Ans1S/esp32-c3-iot-sensor-board/Firmware/sensor/include/environmental_sensor.h

#pragma once

#include "lsm6dsox_driver.h"
#include "precision_sensors.h"
#include "bme280_driver.h"
#include "bme680_driver.h"
#include "environmental_reading.h"
#include "power_controller.h"

namespace sensor {

class EnvironmentalSensor {
 public:
  bool begin(PowerController& power,
             lil::protocol::EnvironmentalSensorType requestedType,
             float temperatureOffsetC);
  EnvironmentalReading read();
  bool pollLive() { return detectedType_ == lil::protocol::EnvironmentalSensorType::kLsm6dsox ? lsm6dsox_.poll() : precision_.poll(); }
  bool freshTemperature() const { return precision_.freshTemperature(); }
  void resetMotionFeedback() { lsm6dsox_.resetFeedback(); }
  void end();
  void prepareForDeepSleep(
      uint32_t seconds,
      lil::protocol::EnvironmentalSensorType activeType =
          lil::protocol::EnvironmentalSensorType::kAutoDetect);
  uint32_t bme680RecommendedSleepSeconds(uint32_t fallbackSeconds) const;
  bool clearIaqState();
  lil::protocol::EnvironmentalSensorType detectedType() const;

 private:
  lil::protocol::EnvironmentalSensorType probeSensorType(uint8_t& address) const;
  bool startDetectedSensor(
      lil::protocol::EnvironmentalSensorType requestedType,
      float temperatureOffsetC);
  bool beginType(lil::protocol::EnvironmentalSensorType type,
                 uint8_t address, float temperatureOffsetC);

  PowerController* power_ = nullptr;
  Lsm6dsoxDriver lsm6dsox_;
  PrecisionSensors precision_;
  Bme280Driver bme280_;
  Bme680Driver bme680_;
  lil::protocol::EnvironmentalSensorType requestedType_ =
      lil::protocol::EnvironmentalSensorType::kAutoDetect;
  lil::protocol::EnvironmentalSensorType detectedType_ =
      lil::protocol::EnvironmentalSensorType::kAutoDetect;
  bool initialized_ = false;
  bool typeMismatch_ = false;
};

}  // namespace sensor
