Ans1S/esp32-c3-iot-sensor-board/Firmware/station/src/web_portal.cpp

#include "web_portal.h"
#include "recording_json.h"
#include "ota_service.h"
#include "ota_page.h"
#include "recording_archive.h"
#include <memory>

#include <ArduinoJson.h>
#include <SHA2Builder.h>
#include <esp_heap_caps.h>
#include <esp_random.h>
#include <esp_timer.h>

#include "web_pages.h"
#include "web_input.h"

namespace station {

namespace {
constexpr size_t kMaxScannedNetworks = 20;
constexpr char kSessionCookieName[] = "wch_session";
constexpr char kPasswordHashDomain[] = "W-Charger website password v1";
constexpr uint8_t kMaxLoginAttempts = 5;
constexpr uint32_t kLoginBlockMs = 30000;
constexpr uint32_t kLoginAttemptWindowMs = 5UL * 60UL * 1000UL;
constexpr uint64_t kSessionLifetimeMs = 30ULL * 60ULL * 1000ULL;
constexpr uint32_t kSessionLifetimeSeconds = kSessionLifetimeMs / 1000UL;

bool readUnsignedArgument(WebServer& server, const char* name,
                          uint32_t& value, uint32_t minimum = 0,
                          uint32_t maximum = UINT32_MAX,
                          bool optional = false) {
  if (!server.hasArg(name)) return optional;
  return webinput::unsignedDecimal(server.arg(name).c_str(), value,
                                  minimum, maximum);
}

bool readFieldArgument(WebServer& server, const char* name, uint8_t& field) {
  uint32_t value = 0;
  if (!readUnsignedArgument(server, name, value, 0, 8, true)) return false;
  field = static_cast<uint8_t>(value);
  return true;
}

void hashAdminPassword(const String& password, char output[65]) {
  SHA256Builder hash;
  hash.begin();
  const uint64_t deviceId = ESP.getEfuseMac();
  hash.add(reinterpret_cast<const uint8_t*>(kPasswordHashDomain),
           strlen(kPasswordHashDomain));
  hash.add(reinterpret_cast<const uint8_t*>(&deviceId), sizeof(deviceId));
  hash.add(reinterpret_cast<const uint8_t*>(password.c_str()),
           password.length());
  hash.calculate();
  hash.getChars(output);
}

bool constantTimeEquals(const char* first, const char* second,
                        size_t length) {
  uint8_t difference = 0;
  for (size_t i = 0; i < length; ++i) {
    difference |= static_cast<uint8_t>(first[i] ^ second[i]);
  }
  return difference == 0;
}

void randomToken(char output[33]) {
  snprintf(output, 33, "%08lX%08lX%08lX%08lX",
           static_cast<unsigned long>(esp_random()),
           static_cast<unsigned long>(esp_random()),
           static_cast<unsigned long>(esp_random()),
           static_cast<unsigned long>(esp_random()));
}

void appendFormValue(String& body, const char* name, const String& value) {
  if (!body.isEmpty()) {
    body += '&';
  }
  body += name;
  body += '=';
  body += ThingSpeakService::urlEncode(value);
}

void extractApiKeys(JsonObjectConst channel, String& readKey,
                    String& writeKey) {
  for (JsonObjectConst key : channel["api_keys"].as<JsonArrayConst>()) {
    if (key["write_flag"] | false) {
      writeKey = key["api_key"].as<String>();
    } else if (readKey.isEmpty()) {
      readKey = key["api_key"].as<String>();
    }
  }
}

String tagsAsText(JsonVariantConst value) {
  String output;
  for (JsonVariantConst tag : value.as<JsonArrayConst>()) {
    const String name = tag.is<JsonObjectConst>()
                            ? tag["name"].as<String>()
                            : tag.as<String>();
    if (name.isEmpty()) {
      continue;
    }
    if (!output.isEmpty()) {
      output += ", ";
    }
    output += name;
  }
  return output;
}

bool validOptionalDecimal(const String& text, double minimum,
                          double maximum) {
  if (text.isEmpty()) {
    return true;
  }
  char* end = nullptr;
  const double value = strtod(text.c_str(), &end);
  return end != text.c_str() && *end == '\0' && isfinite(value) &&
         value >= minimum && value <= maximum;
}

bool validManagedChannelRequest(WebServer& server) {
  if (server.arg("name").isEmpty() || server.arg("name").length() > 80 ||
      server.arg("description").length() > 255 ||
      server.arg("metadata").length() > 512 ||
      server.arg("tags").length() > 160 || server.arg("url").length() > 200 ||
      !validOptionalDecimal(server.arg("latitude"), -90.0, 90.0) ||
      !validOptionalDecimal(server.arg("longitude"), -180.0, 180.0) ||
      !validOptionalDecimal(server.arg("elevation"), -10000.0, 100000.0)) {
    return false;
  }
  for (uint8_t field = 1; field <= 8; ++field) {
    if (server.arg("field" + String(field)).length() > 80) {
      return false;
    }
  }
  return true;
}

String managedChannelSettings(WebServer& server) {
  String body;
  body.reserve(900);
  appendFormValue(body, "name", server.arg("name"));
  appendFormValue(body, "description", server.arg("description"));
  appendFormValue(body, "metadata", server.arg("metadata"));
  appendFormValue(body, "tags", server.arg("tags"));
  appendFormValue(body, "url", server.arg("url"));
  appendFormValue(body, "latitude", server.arg("latitude"));
  appendFormValue(body, "longitude", server.arg("longitude"));
  appendFormValue(body, "elevation", server.arg("elevation"));
  appendFormValue(body, "public_flag",
                  server.hasArg("publicFlag") ? "true" : "false");
  for (uint8_t field = 1; field <= 8; ++field) {
    const String key = "field" + String(field);
    appendFormValue(body, key.c_str(), server.arg(key));
  }
  return body;
}

bool validThingSpeakFields(const ThingSpeakFieldMapping& fields,
                           bool requireOne) {
  const uint8_t values[] = {fields.temperature, fields.humidity,
                            fields.pressure, fields.iaq, fields.battery,
                            fields.gasResistance};
  constexpr size_t count = sizeof(values) / sizeof(values[0]);
  bool hasField = false;
  for (size_t i = 0; i < count; ++i) {
    if (values[i] > 8) {
      return false;
    }
    if (values[i] == 0) {
      continue;
    }
    hasField = true;
    for (size_t j = i + 1; j < count; ++j) {
      if (values[i] == values[j]) {
        return false;
      }
    }
  }
  return hasField || !requireOne;
}

void sendNoCache(WebServer& server) {
  server.sendHeader("Cache-Control", "no-store, no-cache, must-revalidate");
  server.sendHeader("Pragma", "no-cache");
  server.sendHeader("X-Content-Type-Options", "nosniff");
  server.sendHeader("X-Frame-Options", "DENY");
  server.sendHeader("Referrer-Policy", "no-referrer");
  server.sendHeader("Permissions-Policy",
                    "camera=(), microphone=(), geolocation=()");
  server.sendHeader("Cross-Origin-Resource-Policy", "same-origin");
  server.sendHeader(
      "Content-Security-Policy",
      "default-src 'self'; style-src 'self' 'unsafe-inline'; script-src "
      "'self' 'unsafe-inline'; img-src 'self' data:; connect-src 'self'; "
      "object-src 'none'; frame-ancestors 'none'; base-uri 'none'; "
      "form-action 'self'");
}
}  // namespace

bool WebPortal::begin(StationConfig& config, ConfigStore& store,
                      WifiService& wifi, SensorRegistry& registry,
                      ThingSpeakService& thingSpeak, EspNowGateway& gateway) {
  config_ = &config;
  store_ = &store;
  wifi_ = &wifi;
  registry_ = &registry;
  thingSpeak_ = &thingSpeak;
  gateway_ = &gateway;
  refreshCsrfToken();
  clearAuthSessions();
  const char* collectedHeaders[] = {"Cookie", "Origin"};
  server_.collectHeaders(collectedHeaders, 2);

  server_.on("/", HTTP_GET, [this]() {
    sendNoCache(server_);
    if (config_->wifiSsid[0] != '\0' && !requireAuthentication(true)) {
      return;
    }
    server_.send_P(200, "text/html; charset=utf-8",
                   config_->wifiSsid[0] == '\0' ? kSetupWizardPage
                                                : kDashboardPage);
  });
  server_.on("/setup", HTTP_GET, [this]() {
    sendNoCache(server_);
    if (config_->wifiSsid[0] != '\0') {
      server_.sendHeader("Location", "/dashboard", true);
      server_.send(302, "text/plain", "");
      return;
    }
    server_.send_P(200, "text/html; charset=utf-8", kSetupWizardPage);
  });
  server_.on("/dashboard", HTTP_GET, [this]() {
    sendNoCache(server_);
    if (!requireAuthentication(true)) {
      return;
    }
    server_.send_P(200, "text/html; charset=utf-8", kDashboardPage);
  });
  server_.on("/login", HTTP_GET, [this]() { handleLogin(); });
  server_.on("/login", HTTP_POST, [this]() { handleLogin(); });
  server_.on("/logout", HTTP_POST, [this]() {
    if (requireAuthentication() && verifyCsrf()) handleLogout();
  });
  server_.on("/api/status", HTTP_GET, [this]() {
    if (requireAuthentication()) sendJsonStatus();
  });
  server_.on("/api/ota", HTTP_GET, [this]() {
    if (!requireAuthentication()) return;
    JsonDocument doc;
    otaService.json(doc.to<JsonObject>());
    String body; serializeJson(doc, body);
    sendNoCache(server_); server_.send(200, "application/json", body);
  });
  server_.on("/updates", HTTP_GET, [this]() {
    if (!requireAuthentication(true)) return;
    sendNoCache(server_); server_.send_P(200, "text/html; charset=utf-8", kOtaPage);
  });
  server_.on("/api/ota/cancel", HTTP_POST, [this]() {
    if (requireAuthentication() && verifyCsrf())
      sendJsonResult(otaService.cancel(), "Update cancellation saved; a reboot already initiated cannot be cancelled");
  });
  server_.on("/api/ota/upload", HTTP_POST, [this]() {
    if (!otaUploadAuthorized_) return;
    sendJsonResult(otaUploadOk_, otaUploadOk_ ? "Update queued for the next node contact" : otaUploadError_);
    otaUploadAuthorized_ = false;
  }, [this]() {
    HTTPUpload& upload = server_.upload();
    if (upload.status == UPLOAD_FILE_START) {
      otaUploadAuthorized_ = requireAuthentication() && verifyCsrf();
      otaUploadOk_ = false; otaUploadError_ = "Upload failed";
      if (!otaUploadAuthorized_) return;
      uint8_t mac[6];
      if (!SensorRegistry::parseMac(server_.arg("mac"), mac)) {
        otaUploadError_ = "Invalid node address"; return;
      }
      SensorConfig node{};
      if (!registry_->findConfig(mac, node) || !node.provisioned) {
        otaUploadError_ = "Select a configured node"; return;
      }
      otaUploadOk_ = otaService.startUpload(mac, otaUploadError_);
    } else if (upload.status == UPLOAD_FILE_WRITE && otaUploadAuthorized_ && otaUploadOk_) {
      if (!otaService.upload(upload.buf, upload.currentSize)) {
        otaUploadOk_ = false; otaUploadError_ = "Firmware exceeds capacity or flash write failed";
        otaService.abortUpload();
      }
    } else if (upload.status == UPLOAD_FILE_END && otaUploadAuthorized_ && otaUploadOk_) {
      otaUploadOk_ = otaService.finishUpload(otaUploadError_);
    } else if (upload.status == UPLOAD_FILE_ABORTED && otaUploadAuthorized_) {
      otaService.abortUpload(); otaUploadOk_ = false;
    }
  });
  server_.on("/api/history", HTTP_GET, [this]() {
    if (requireAuthentication()) sendJsonHistory();
  });
  server_.on("/api/recordings", HTTP_GET, [this]() { if (requireAuthentication()) sendRecordings(); });
  server_.on("/api/recording", HTTP_GET, [this]() { if (requireAuthentication()) sendRecording(); });
  server_.on("/api/motion-reference", HTTP_POST, [this]() { if (requireAuthentication() && verifyCsrf()) setMotionReference(); });
  server_.on("/api/recording/delete", HTTP_POST, [this]() {
    if (requireAuthentication() && verifyCsrf()) deleteRecording();
  });
  server_.on("/api/config", HTTP_GET, [this]() {
    if (requireAuthentication()) sendJsonConfig();
  });
  server_.on("/api/wifi-scan", HTTP_GET, [this]() {
    if (requireAuthentication()) sendWifiScan();
  });
  server_.on("/api/setup", HTTP_POST, [this]() {
    if (requireAuthentication() && verifyCsrf()) saveSetup();
  });
  server_.on("/api/setup-sensor", HTTP_POST, [this]() {
    if (requireAuthentication() && verifyCsrf()) saveSetupSensor();
  });
  server_.on("/api/station", HTTP_POST, [this]() {
    if (requireAuthentication() && verifyCsrf()) saveStation();
  });
  server_.on("/api/sensor", HTTP_POST, [this]() {
    if (requireAuthentication() && verifyCsrf()) saveSensor();
  });
  server_.on("/api/channel-profile", HTTP_POST, [this]() {
    if (requireAuthentication() && verifyCsrf()) saveChannelProfile();
  });
  server_.on("/api/delete-channel-profile", HTTP_POST, [this]() {
    if (requireAuthentication() && verifyCsrf()) deleteChannelProfile();
  });
  server_.on("/api/create-channel", HTTP_POST, [this]() {
    if (requireAuthentication() && verifyCsrf()) createThingSpeakChannel();
  });
  server_.on("/api/thingspeak/channels", HTTP_GET, [this]() {
    if (requireAuthentication()) listThingSpeakChannels();
  });
  server_.on("/api/thingspeak/channel-create", HTTP_POST, [this]() {
    if (requireAuthentication() && verifyCsrf())
      createManagedThingSpeakChannel();
  });
  server_.on("/api/thingspeak/channel-update", HTTP_POST, [this]() {
    if (requireAuthentication() && verifyCsrf())
      updateManagedThingSpeakChannel();
  });
  server_.on("/api/thingspeak/channel-clear", HTTP_POST, [this]() {
    if (requireAuthentication() && verifyCsrf())
      clearManagedThingSpeakChannel();
  });
  server_.on("/api/thingspeak/channel-delete", HTTP_POST, [this]() {
    if (requireAuthentication() && verifyCsrf())
      deleteManagedThingSpeakChannel();
  });
  server_.on("/api/reset-sensor", HTTP_POST, [this]() {
    if (requireAuthentication() && verifyCsrf()) resetSensor();
  });
  server_.on("/api/reset-sensor-iaq", HTTP_POST, [this]() {
    if (requireAuthentication() && verifyCsrf()) resetSensorIaqCalibration();
  });
  server_.on("/api/delete-sensor", HTTP_POST, [this]() {
    if (requireAuthentication() && verifyCsrf()) deleteSensor();
  });
  server_.on("/api/factory-reset", HTTP_POST, [this]() {
    if (requireAuthentication() && verifyCsrf()) factoryReset();
  });
  server_.on("/favicon.ico", HTTP_GET, [this]() {
    sendNoCache(server_);
    server_.send(204, "text/plain", "");
  });

  const auto captiveRedirect = [this]() {
    sendNoCache(server_);
    server_.sendHeader("Connection", "close");
    server_.sendHeader("Location", "/", true);
    server_.send(302, "text/plain", "");
  };
  server_.on("/generate_204", HTTP_ANY, captiveRedirect);
  server_.on("/gen_204", HTTP_ANY, captiveRedirect);
  server_.on("/hotspot-detect.html", HTTP_ANY, captiveRedirect);
  server_.on("/library/test/success.html", HTTP_ANY, captiveRedirect);
  server_.on("/fwlink", HTTP_ANY, captiveRedirect);
  server_.on("/connecttest.txt", HTTP_ANY, captiveRedirect);
  server_.on("/redirect", HTTP_ANY, captiveRedirect);
  server_.on("/canonical.html", HTTP_ANY, captiveRedirect);
  server_.on("/success.txt", HTTP_ANY, captiveRedirect);
  server_.on("/ncsi.txt", HTTP_ANY, captiveRedirect);
  // Common HTTP-only connectivity probes. HTTPS probes cannot be redirected
  // safely because the device does not own their TLS certificates; users can
  // always open http://192.168.4.1/ directly in that case.
  server_.on("/connectivity-check.html", HTTP_ANY, captiveRedirect);
  server_.on("/check_network_status.txt", HTTP_ANY, captiveRedirect);
  server_.on("/portal.html", HTTP_ANY, captiveRedirect);
  server_.on("/success.html", HTTP_ANY, captiveRedirect);
  server_.on("/wifi/wifidog", HTTP_ANY, captiveRedirect);
  server_.on("/kindle-wifi/wifistub.html", HTTP_ANY, captiveRedirect);
  server_.on("/.well-known/captive-portal", HTTP_ANY, captiveRedirect);
  server_.onNotFound([this, captiveRedirect]() {
    const bool apiPath = server_.uri().startsWith("/api/");
    if (apiPath ||
        (config_->wifiSsid[0] != '\0' && !wifi_->setupPortalActive())) {
      sendNoCache(server_);
      server_.send(404, apiPath ? "application/json" : "text/plain",
                   apiPath
                       ? "{\"success\":false,\"message\":\"Not found\"}"
                       : "Not found");
      return;
    }
    captiveRedirect();
  });
  server_.begin();
  return true;
}

bool WebPortal::authenticationEnabled() const {
  return config_ != nullptr && config_->adminPassword[0] != '\0';
}

String WebPortal::currentSessionToken() const {
  const String cookies = server_.header("Cookie");
  const String prefix = String(kSessionCookieName) + '=';
  int start = 0;
  while (start < static_cast<int>(cookies.length())) {
    int end = cookies.indexOf(';', start);
    if (end < 0) {
      end = cookies.length();
    }
    String cookie = cookies.substring(start, end);
    cookie.trim();
    if (cookie.startsWith(prefix)) {
      return cookie.substring(prefix.length());
    }
    start = end + 1;
  }
  return String();
}

bool WebPortal::isAuthenticated() {
  if (!authenticationEnabled()) {
    return true;
  }
  const String token = currentSessionToken();
  if (token.length() != 32) {
    return false;
  }
  const uint64_t now = static_cast<uint64_t>(esp_timer_get_time()) / 1000ULL;
  for (AuthSession& session : authSessions_) {
    if (!session.active) {
      continue;
    }
    if (now - session.createdAtMs >= kSessionLifetimeMs) {
      session = AuthSession{};
      continue;
    }
    if (constantTimeEquals(token.c_str(), session.token, 32)) {
      return true;
    }
  }
  return false;
}

bool WebPortal::requireAuthentication(bool redirectToLogin) {
  if (isAuthenticated()) {
    return true;
  }
  sendNoCache(server_);
  if (redirectToLogin) {
    server_.sendHeader("Location", "/login", true);
    server_.send(302, "text/plain", "");
  } else {
    JsonDocument document;
    document["success"] = false;
    document["message"] = "Authentication required";
    document["authenticationRequired"] = true;
    String output;
    serializeJson(document, output);
    server_.send(401, "application/json", output);
  }
  return false;
}

bool WebPortal::verifyAdminPassword(const String& password) const {
  if (!authenticationEnabled() || password.length() > 64) {
    return false;
  }
  char candidate[65]{};
  hashAdminPassword(password, candidate);
  return constantTimeEquals(candidate, config_->adminPassword, 64);
}

void WebPortal::setAdminPassword(const String& password) {
  if (password.isEmpty()) {
    config_->adminPassword[0] = '\0';
    return;
  }
  hashAdminPassword(password, config_->adminPassword);
}

void WebPortal::refreshCsrfToken() { randomToken(csrfToken_); }

const char* WebPortal::createAuthSession() {
  const uint64_t now = static_cast<uint64_t>(esp_timer_get_time()) / 1000ULL;
  size_t selected = 0;
  uint64_t oldestAge = 0;
  for (size_t i = 0; i < 4; ++i) {
    AuthSession& session = authSessions_[i];
    if (session.active && now - session.createdAtMs >= kSessionLifetimeMs) {
      session = AuthSession{};
    }
    if (!session.active) {
      selected = i;
      break;
    }
    const uint64_t age = now - session.createdAtMs;
    if (i == 0 || age > oldestAge) {
      selected = i;
      oldestAge = age;
    }
  }
  AuthSession& session = authSessions_[selected];
  randomToken(session.token);
  session.createdAtMs = now;
  session.active = true;
  return session.token;
}

void WebPortal::clearAuthSessions() {
  for (AuthSession& session : authSessions_) {
    session = AuthSession{};
  }
}

void WebPortal::revokeCurrentSession() {
  const String token = currentSessionToken();
  if (token.length() != 32) {
    return;
  }
  for (AuthSession& session : authSessions_) {
    if (session.active &&
        constantTimeEquals(token.c_str(), session.token, 32)) {
      session = AuthSession{};
      return;
    }
  }
}

bool WebPortal::loginBlocked(uint32_t& retryAfterSeconds) {
  LoginThrottle& throttle = loginThrottle_;
  const uint32_t now = millis();
  if (throttle.blockedUntilMs != 0 &&
      static_cast<int32_t>(now - throttle.blockedUntilMs) < 0) {
    retryAfterSeconds =
        (throttle.blockedUntilMs - now + 999UL) / 1000UL;
    return true;
  }
  if (throttle.blockedUntilMs != 0 ||
      now - throttle.lastAttemptMs > kLoginAttemptWindowMs) {
    throttle.blockedUntilMs = 0;
    throttle.failures = 0;
  }
  retryAfterSeconds = 0;
  return false;
}

bool WebPortal::recordFailedLogin(uint32_t& retryAfterSeconds) {
  LoginThrottle& throttle = loginThrottle_;
  const uint32_t now = millis();
  if (now - throttle.lastAttemptMs > kLoginAttemptWindowMs) {
    throttle.failures = 0;
  }
  throttle.lastAttemptMs = now;
  ++throttle.failures;
  if (throttle.failures < kMaxLoginAttempts) {
    retryAfterSeconds = 0;
    return false;
  }
  throttle.failures = 0;
  throttle.blockedUntilMs = now + kLoginBlockMs;
  retryAfterSeconds = kLoginBlockMs / 1000UL;
  return true;
}

void WebPortal::clearLoginFailures() {
  loginThrottle_ = LoginThrottle{};
}

bool WebPortal::validRequestOrigin() const {
  const String origin = server_.header("Origin");
  if (origin.isEmpty()) {
    return true;
  }
  const String host = server_.hostHeader();
  return !host.isEmpty() &&
         (origin.equalsIgnoreCase("http://" + host) ||
          origin.equalsIgnoreCase("https://" + host));
}

void WebPortal::handleLogin() {
  sendNoCache(server_);
  if (!authenticationEnabled()) {
    server_.sendHeader("Location", "/dashboard", true);
    server_.send(302, "text/plain", "");
    return;
  }
  if (server_.method() == HTTP_GET) {
    if (isAuthenticated()) {
      server_.sendHeader("Location", "/dashboard", true);
      server_.send(302, "text/plain", "");
      return;
    }
    server_.send_P(200, "text/html; charset=utf-8", kLoginPage);
    return;
  }

  if (!validRequestOrigin()) {
    JsonDocument document;
    document["success"] = false;
    document["message"] = "Request origin is not allowed";
    String output;
    serializeJson(document, output);
    server_.send(403, "application/json", output);
    return;
  }

  uint32_t retryAfterSeconds = 0;
  if (loginBlocked(retryAfterSeconds)) {
    server_.sendHeader("Retry-After", String(retryAfterSeconds));
    JsonDocument document;
    document["success"] = false;
    document["message"] = "Too many attempts. Try again in a few seconds.";
    String output;
    serializeJson(document, output);
    server_.send(429, "application/json", output);
    return;
  }
  if (!verifyAdminPassword(server_.arg("password"))) {
    const bool nowBlocked = recordFailedLogin(retryAfterSeconds);
    JsonDocument document;
    document["success"] = false;
    document["message"] = nowBlocked
                              ? "Too many attempts. Try again in 30 seconds."
                              : "Incorrect password";
    String output;
    serializeJson(document, output);
    if (nowBlocked) {
      server_.sendHeader("Retry-After", String(retryAfterSeconds));
    }
    server_.send(nowBlocked ? 429 : 401, "application/json", output);
    return;
  }

  clearLoginFailures();
  const char* sessionToken = createAuthSession();
  server_.sendHeader(
      "Set-Cookie",
      String(kSessionCookieName) + '=' + sessionToken +
          "; Path=/; Max-Age=" + String(kSessionLifetimeSeconds) +
          "; HttpOnly; SameSite=Strict");
  server_.send(200, "application/json", "{\"success\":true}");
}

void WebPortal::handleLogout() {
  sendNoCache(server_);
  revokeCurrentSession();
  server_.sendHeader(
      "Set-Cookie",
      String(kSessionCookieName) +
          "=; Path=/; Max-Age=0; HttpOnly; SameSite=Strict");
  server_.send(200, "application/json", "{\"success\":true}");
}

bool WebPortal::verifyCsrf() {
  if (!validRequestOrigin()) {
    sendNoCache(server_);
    server_.send(
        403, "application/json",
        "{\"success\":false,\"message\":\"Request origin is not allowed\"}");
    return false;
  }
  if (server_.arg("csrf") == csrfToken_) {
    return true;
  }
  sendNoCache(server_);
  server_.send(403, "application/json",
               "{\"success\":false,\"message\":\"Invalid CSRF token\"}");
  return false;
}

void WebPortal::loop() {
  server_.handleClient();
  if (restartAtMs_ != 0 && static_cast<int32_t>(millis() - restartAtMs_) >= 0) {
    ESP.restart();
  }
}

void WebPortal::sendJsonStatus() {
  JsonDocument document;
  document["storageAvailable"] = store_->storageAvailable();
  document["uptimeMs"] = millis();
  document["freeHeap"] = ESP.getFreeHeap();
  JsonObject wifi = document["wifi"].to<JsonObject>();
  wifi["connected"] = wifi_->stationConnected();
  wifi["ssid"] = wifi_->stationSsid();
  wifi["ip"] = wifi_->stationIp();
  wifi["apActive"] = wifi_->setupPortalActive();
  wifi["apIp"] = wifi_->accessPointIp();
  wifi["apSsid"] = wifi_->accessPointSsid();
  wifi["channel"] = wifi_->channel();
  wifi["hostname"] = "w-charger";

  JsonObject espnow = document["espnow"].to<JsonObject>();
  espnow["received"] = gateway_->receivedPackets();
  espnow["invalid"] = gateway_->invalidPackets();
  espnow["dropped"] = gateway_->droppedPackets();
  espnow["persistenceDrops"] = gateway_->persistenceDrops();
  espnow["peerFailures"] = gateway_->peerFailures();
  JsonObject cloud = document["cloud"].to<JsonObject>();
  cloud["lastHttpStatus"] = thingSpeak_->lastHttpStatus();
  cloud["lastEntryId"] = thingSpeak_->lastEntryId();
  cloud["successfulUploads"] = thingSpeak_->successfulUploads();
  cloud["failedUploads"] = thingSpeak_->failedUploads();
  cloud["lastAttemptAgeMs"] =
      thingSpeak_->lastAttemptMs() == 0
          ? 0
          : millis() - thingSpeak_->lastAttemptMs();
  cloud["lastSuccessAgeMs"] =
      thingSpeak_->lastSuccessMs() == 0
          ? 0
          : millis() - thingSpeak_->lastSuccessMs();
  cloud["droppedJobs"] = thingSpeak_->droppedJobs();

  // WebServer handlers are serialized; keep the enlarged snapshots off the task stack.
  static SensorView sensorViews[kMaxSensors];
  const size_t count = registry_->views(sensorViews, kMaxSensors);
  size_t provisionedCount = 0;
  size_t pendingCount = 0;
  size_t uploadEnabledCount = 0;
  JsonArray sensors = document["sensors"].to<JsonArray>();
  for (size_t i = 0; i < count; ++i) {
    const SensorView& view = sensorViews[i];
    const bool batteryProtection =
        (view.runtime.telemetry.flags & lil::protocol::kBatteryProtectionActive) != 0;
    const bool recordingActive = view.runtime.hasRecordingStatus &&
        view.runtime.recording.state == lil::recording::State::Recording;
    const bool periodicPrecision =
        (view.runtime.telemetry.sensorType == lil::protocol::EnvironmentalSensorType::kLsm6dsox ||
         view.runtime.telemetry.sensorType == lil::protocol::EnvironmentalSensorType::kTmp117) &&
        !recordingActive;
    const uint32_t ageMs = view.runtime.hasTelemetry
                               ? millis() - view.runtime.lastSeenMs
                               : 0;
    const uint32_t onlineLimitMs =
        batteryProtection ? 26UL * 60UL * 60UL * 1000UL :
        lil::protocol::isLiveSensor(view.runtime.telemetry.sensorType) && !periodicPrecision ? 15000UL :
        max(view.config.sleepSeconds < 60 ? 5000UL : 120000UL, view.config.sleepSeconds * 3000UL);
    JsonObject item = sensors.add<JsonObject>();
    item["mac"] = SensorRegistry::formatMac(view.config.mac);
    item["name"] = view.config.name;
    item["sleepSeconds"] = view.config.sleepSeconds;
    item["revision"] = view.config.revision;
    item["provisioned"] = view.config.provisioned;
    item["profileSlot"] = view.config.thingSpeakProfileSlot;
    item["channelId"] = view.config.thingSpeakChannelId;
    item["uploadEnabled"] = view.config.cloudUploadEnabled;
    item["writeKeySet"] = view.config.thingSpeakWriteKey[0] != '\0';
    item["temperatureField"] = view.config.thingSpeakFields.temperature;
    item["humidityField"] = view.config.thingSpeakFields.humidity;
    item["pressureField"] = view.config.thingSpeakFields.pressure;
    item["iaqField"] = view.config.thingSpeakFields.iaq;
    item["batteryField"] = view.config.thingSpeakFields.battery;
    item["gasResistanceField"] =
        view.config.thingSpeakFields.gasResistance;
    item["configuredSensorType"] =
        static_cast<uint8_t>(view.config.environmentalSensorType);
    item["configPending"] = !view.runtime.hasTelemetry ||
        view.runtime.telemetry.appliedConfigRevision != view.config.revision;
    item["sensorType"] =
        static_cast<uint8_t>(view.runtime.telemetry.sensorType);
    item["temperatureOffsetC"] = view.config.temperatureOffsetC;
    item["batteryCalibrationFactor"] =
        view.config.batteryCalibrationFactor;
    item["seen"] = view.runtime.hasTelemetry;
    item["restored"] = view.runtime.hasPersistedTelemetry;
    item["online"] = view.runtime.hasTelemetry && ageMs <= onlineLimitMs;
    item["ageMs"] = ageMs;
    item["rssi"] = view.runtime.stationRssi;
    item["sensorTxPowerDbm"] =
        static_cast<float>(view.runtime.sensorTxPowerQuarterDbm) / 4.0F;
    const auto& timing = view.runtime.telemetry.live;
    item["timingKnown"] = (timing.flags & lil::protocol::kLiveTimingKnown) != 0;
    item["acquisitionAgeMs"] = timing.acquisitionAgeMs == UINT16_MAX ? -1 : int64_t(timing.acquisitionAgeMs) + ageMs;
    item["estimateAgeMs"] = timing.estimateAgeMs == UINT16_MAX ? -1 : int64_t(timing.estimateAgeMs) + ageMs;
    item["measurementWindowMs"] = timing.windowMs;
    item["warmupMs"] = timing.warmupMs;
    item["processingMs"] = timing.processingMs;
    item["receivedIntervalMs"] = view.runtime.receivedIntervalMs;
    if (view.runtime.hasRecordingStatus && !batteryProtection) {
      const auto& recording = view.runtime.recording;
      auto r = item["recording"].to<JsonObject>();
      r["state"] = static_cast<uint8_t>(recording.state);
      r["pending"] = recording.pending; r["capacity"] = recording.capacity;
      r["elapsedMs"] = recording.elapsedMs; r["dropped"] = recording.dropped;
      char session[17]; snprintf(session, sizeof(session), "%016llx", static_cast<unsigned long long>(recording.session));
      r["session"] = session;
    }
    const auto& pulse = view.runtime.telemetry.pulse;
    item["heartRate"] = (view.runtime.telemetry.capabilities & lil::protocol::kHeartRate) ? pulse.beatsPerMinute : 0;
    item["red"] = pulse.red; item["infrared"] = pulse.infrared;
    item["pulseQuality"] = pulse.quality; item["pulseStatus"] = pulse.status;
    item["live"] = !batteryProtection && lil::protocol::isLiveSensor(view.runtime.telemetry.sensorType);
    item["batteryProtection"] = batteryProtection;
    item["liveRevision"] = view.runtime.receivedPackets;
    item["normalSampling"] = periodicPrecision;
    item["reportIntervalMs"] = batteryProtection ? 86400000UL : lil::protocol::isLiveSensor(view.runtime.telemetry.sensorType) && !periodicPrecision ?
        (view.runtime.telemetry.sensorType == lil::protocol::EnvironmentalSensorType::kLsm6dsox && recordingActive ?
            lil::timing::imuRecordingIntervalMs(view.runtime.recording.elapsedMs) :
            lil::protocol::liveReportIntervalMs(view.runtime.telemetry.sensorType)) : view.config.sleepSeconds * 1000;
    const auto& motion = view.runtime.telemetry.motion;
    auto reference = item["motionReference"].to<JsonObject>();
    reference["enabled"] = view.motionReference.enabled;
    const char* accelerationKeys[] = {"ax", "ay", "az"};
    const char* angularKeys[] = {"gx", "gy", "gz"};
    for (size_t axis = 0; axis < 3; ++axis) {
      item[accelerationKeys[axis]] = motion.accelerationG[axis];
      item[angularKeys[axis]] = motion.angularRateDps[axis];
      reference[accelerationKeys[axis]] = view.motionReference.accelerationG[axis];
      reference[angularKeys[axis]] = view.motionReference.angularRateDps[axis];
    }
    item["peakAcceleration"] = motion.peakAccelerationG;
    item["peakAngularRate"] = motion.peakAngularRateDps;
    item["motionSamples"] = motion.sampleCount;
    item["motionOverrun"] = motion.fifoOverrun != 0;
    item["temperature"] = view.runtime.telemetry.temperatureC;
    item["humidity"] = view.runtime.telemetry.humidityPercent;
    item["pressure"] = view.runtime.telemetry.pressureHpa;
    item["iaq"] = view.runtime.telemetry.iaq;
    item["iaqAccuracy"] = view.runtime.telemetry.iaqAccuracy;
    item["iaqCalibrationPhase"] = static_cast<uint8_t>(
        view.runtime.telemetry.iaqCalibrationPhase);
    item["iaqCalibrationElapsedMinutes"] =
        view.runtime.telemetry.iaqCalibrationElapsedMinutes;
    item["iaqCalibrationRemainingMinutes"] =
        view.runtime.telemetry.iaqCalibrationRemainingMinutes;
    item["bme680QuickStartComplete"] =
        view.config.bme680QuickStartComplete;
    item["gasResistanceOhms"] =
        view.runtime.telemetry.gasResistanceOhms;
    item["capabilities"] = view.runtime.telemetry.capabilities;
    item["telemetryFlags"] = view.runtime.telemetry.flags;
    item["batteryMv"] = view.runtime.telemetry.batteryMillivolts;
    item["pcbVersion"] = view.runtime.telemetry.pcbVersion;
    item["operatingMode"] = static_cast<uint8_t>(
        (view.runtime.hasTelemetry || view.runtime.hasPersistedTelemetry)
            ? view.runtime.telemetry.operatingMode
            : lil::protocol::SensorOperatingMode::kUnknown);
    item["appliedRevision"] = view.runtime.telemetry.appliedConfigRevision;
    item["historyRevision"] = registry_->historyRevision(view.config.mac);
    if (view.config.provisioned) {
      ++provisionedCount;
      if (view.config.cloudUploadEnabled) {
        ++uploadEnabledCount;
      }
    } else {
      ++pendingCount;
    }
  }
  cloud["configuredSensors"] = provisionedCount;
  cloud["pendingSensors"] = pendingCount;
  cloud["uploadEnabledSensors"] = uploadEnabledCount;

  String output;
  serializeJson(document, output);
  sendNoCache(server_);
  server_.send(200, "application/json", output);
}


namespace {
uint64_t recordingSession(const String& text) {
  if (text.length() != 16) return 0;
  for (size_t i = 0; i < text.length(); ++i) if (!isxdigit(static_cast<unsigned char>(text[i]))) return 0;
  return strtoull(text.c_str(), nullptr, 16);
}

}
void WebPortal::sendRecordings() {
  uint8_t mac[6]{}; SensorConfig config{};
  if (!SensorRegistry::parseMac(server_.arg("mac"), mac) || !registry_->findConfig(mac, config)) {
    sendJsonResult(false, "Sensor not found"); return;
  }
  JsonDocument doc; doc["freeBytes"] = recordingArchive.freeBytes();
  auto sessions = doc["sessions"].to<JsonArray>();
  for (const auto& info : recordingArchive.list(mac)) recordingInfoJson(sessions.add<JsonObject>(), info);
  String json; serializeJson(doc, json); sendNoCache(server_); server_.send(200, "application/json", json);
}
void WebPortal::sendRecording() {
  uint8_t mac[6]{}; SensorConfig config{};
  const uint64_t session = recordingSession(server_.arg("session"));
  if (!session || !SensorRegistry::parseMac(server_.arg("mac"), mac) || !registry_->findConfig(mac, config)) {
    sendJsonResult(false, "Invalid recording"); return;
  }
  std::unique_ptr<lil::recording::Record[]> records(new (std::nothrow) lil::recording::Record[128]);
  if (!records) { sendJsonResult(false, "Recording buffer unavailable"); return; }
  uint32_t offset = 0, fromMs = UINT32_MAX;
  if (!readUnsignedArgument(server_, "offset", offset, 0, UINT32_MAX, true) ||
      !readUnsignedArgument(server_, "fromMs", fromMs, 0, UINT32_MAX, true)) {
    sendJsonResult(false, "Invalid recording cursor"); return;
  }
  RecordingInfo info{};
  const size_t count = recordingArchive.read(mac, session, offset, records.get(), 128, info, fromMs);
  if (!info.session) { sendJsonResult(false, "Recording not found"); return; }
  if (info.readError) { sendJsonResult(false, "Stored recording failed CRC validation. Synchronize again before exporting."); return; }
  JsonDocument metadata; recordingInfoJson(metadata.to<JsonObject>(), info);
  metadata["nextOffset"] = offset;
  String opening; serializeJson(metadata, opening); opening.remove(opening.length()-1);
  sendNoCache(server_); server_.setContentLength(CONTENT_LENGTH_UNKNOWN); server_.send(200, "application/json", "");
  // Batch points to avoid a TCP/chunked-response write for every JSON field group.
  String chunk = opening + ",\"points\":[";
  chunk.reserve(6144);
  for (size_t i = 0; i < count; ++i) {
    JsonDocument point; recordingPointJson(point, records[i]);
    if (i) chunk += ',';
    appendRecordingJson(point, chunk);
    if (chunk.length() >= 4096) { server_.sendContent(chunk); chunk = ""; }
  }
  chunk += "]}";
  server_.sendContent(chunk); server_.sendContent("");
}
void WebPortal::deleteRecording() {
  uint8_t mac[6]{}; SensorView view{};
  const uint64_t session = recordingSession(server_.arg("session"));
  if (!session || !SensorRegistry::parseMac(server_.arg("mac"), mac) || !registry_->findView(mac, view)) {
    sendJsonResult(false, "Invalid recording"); return;
  }
  // A partial session still being replayed cannot be removed underneath ACKs.
  if (view.runtime.hasRecordingStatus && view.runtime.recording.session == session &&
      view.runtime.recording.pending) { sendJsonResult(false, "Wait for synchronization or start a replacement recording on the sensor"); return; }
  sendJsonResult(recordingArchive.remove(mac, session), "Recording deleted");
}

void WebPortal::setMotionReference() {
  uint8_t mac[6]{};
  const bool clear = server_.arg("clear") == "1";
  const bool saved = SensorRegistry::parseMac(server_.arg("mac"), mac) && registry_->setMotionReference(mac, clear);
  sendJsonResult(saved, saved ? (clear ? "Motion reference cleared." : "All six axes are now relative to this resting position.") :
      "Could not set the reference. Keep the sensor still on the table and wait for a fresh motion reading.");
}

void WebPortal::sendJsonHistory() {
  uint32_t afterMs = 0, since = 0;
  if (!readUnsignedArgument(server_, "afterMs", afterMs, 0, UINT32_MAX, true) ||
      !readUnsignedArgument(server_, "since", since, 0, UINT32_MAX, true)) {
    sendJsonResult(false, "Invalid history cursor"); return;
  }
  uint8_t mac[6]{};
  if (!SensorRegistry::parseMac(server_.arg("mac"), mac)) {
    sendJsonResult(false, "Invalid sensor MAC address");
    return;
  }
  SensorConfig config{};
  if (!registry_->findConfig(mac, config)) {
    sendJsonResult(false, "Sensor not found");
    return;
  }

  SensorView liveView{};
  if (registry_->findView(mac, liveView) && lil::protocol::isLiveSensor(liveView.runtime.telemetry.sensorType) &&
      !(liveView.runtime.telemetry.flags & lil::protocol::kBatteryProtectionActive)) {
    const size_t liveCapacity = 60000 / lil::protocol::liveHistoryIntervalMs(liveView.runtime.telemetry.sensorType) + 1;
    auto* samples = static_cast<LiveSample*>(heap_caps_malloc(liveCapacity * sizeof(LiveSample), MALLOC_CAP_SPIRAM | MALLOC_CAP_8BIT));
    if (!samples && heap_caps_get_free_size(MALLOC_CAP_INTERNAL | MALLOC_CAP_8BIT) > liveCapacity * sizeof(LiveSample) + 96U * 1024U)
      samples = static_cast<LiveSample*>(heap_caps_malloc(liveCapacity * sizeof(LiveSample), MALLOC_CAP_8BIT));
    if (!samples) { sendJsonResult(false, "Live history is temporarily unavailable"); return; }
    const size_t count = registry_->liveHistory(mac, samples, liveCapacity);
    const uint32_t now = millis();
    sendNoCache(server_); server_.setContentLength(CONTENT_LENGTH_UNKNOWN);
    server_.send(200, "application/json", "");
    server_.sendContent(String("{\"live\":true,\"bucketSeconds\":") +
        String(lil::protocol::liveReportIntervalMs(liveView.runtime.telemetry.sensorType) / 1000.0F, 1) + ",\"points\":[");
    size_t emitted = 0;
    for (size_t i = 0; i < count; ++i) {
      if (server_.hasArg("afterMs") && static_cast<int32_t>(samples[i].receivedMs - afterMs) <= 0) continue;
      const auto& sample = samples[i]; const auto& t = sample.telemetry;
      JsonDocument doc;
      doc["id"] = sample.receivedMs;
      doc["sensorType"] = static_cast<uint8_t>(t.sensorType);
      doc["ageMs"] = uint32_t(now - sample.receivedMs);
      const bool timed = t.live.flags & lil::protocol::kLiveTimingKnown;
      doc["measurementAgeMs"] = uint32_t(now - sample.receivedMs) + (timed && t.live.acquisitionAgeMs != UINT16_MAX ? t.live.acquisitionAgeMs : 0);
      doc["windowMs"] = t.live.windowMs;
      doc["estimateAgeMs"] = uint32_t(now - sample.receivedMs) + (timed && t.live.estimateAgeMs != UINT16_MAX ? t.live.estimateAgeMs : 0);
      doc["gap"] = t.motion.fifoOverrun || (t.live.flags & lil::protocol::kLiveGap);
      if (timed && t.live.count <= lil::protocol::kOpticalBatchSize) {
        JsonArray wave = doc["wave"].to<JsonArray>();
        for (uint8_t j = 0; j < t.live.count; ++j) {
          JsonObject frame = wave.add<JsonObject>();
          frame["ageMs"] = uint32_t(now - sample.receivedMs) + t.live.optical[j].ageMs;
          frame["red"] = t.live.optical[j].red; frame["infrared"] = t.live.optical[j].infrared;
        }
      }
      if (!(t.flags & lil::protocol::kSensorReadFailed)) {
        if ((t.capabilities & lil::protocol::kTemperature) && (!timed || (t.live.flags & lil::protocol::kLiveSampleFresh))) doc["temperature"] = t.temperatureC;
        if ((t.capabilities & lil::protocol::kMotion) && !t.motion.fifoOverrun) {
          const char* keys[] = {"ax", "ay", "az", "gx", "gy", "gz"};
          for (int axis = 0; axis < 6; ++axis) doc[keys[axis]] = axis < 3 ? t.motion.accelerationG[axis] : t.motion.angularRateDps[axis-3];
          doc["peakAcceleration"] = t.motion.peakAccelerationG;
          doc["peakAngularRate"] = t.motion.peakAngularRateDps;
        }
        if (t.capabilities & lil::protocol::kOptical) { doc["red"] = t.pulse.red; doc["infrared"] = t.pulse.infrared; }
        if ((t.capabilities & lil::protocol::kHeartRate) && (!timed || (t.live.flags & lil::protocol::kLiveEstimateFresh))) doc["heartRate"] = t.pulse.beatsPerMinute;
      }
      doc["motionOverrun"] = t.motion.fifoOverrun;
      doc["pulseStatus"] = t.pulse.status;
      doc["quality"] = t.pulse.quality;
      if (t.live.flags & lil::protocol::kMotionFeedbackPresent) {
        doc["steps"] = t.motionFeedback.steps;
        doc["activeSeconds"] = t.motionFeedback.activeSeconds;
      }
      if (t.capabilities & lil::protocol::kBattery) doc["battery"] = t.batteryMillivolts / 1000.0F;
      String point; serializeJson(doc, point);
      if (emitted++) server_.sendContent(",");
      server_.sendContent(point);
    }
    heap_caps_free(samples); server_.sendContent("]}"); server_.sendContent(""); return;
  }
  const size_t capacity = registry_->historyCapacity(mac);
  HistorySample* samples = nullptr;
  if (capacity > 0) {
    samples = static_cast<HistorySample*>(heap_caps_malloc(
        capacity * sizeof(HistorySample),
        MALLOC_CAP_SPIRAM | MALLOC_CAP_8BIT));
    if (samples == nullptr &&
        heap_caps_get_free_size(MALLOC_CAP_INTERNAL | MALLOC_CAP_8BIT) >
            capacity * sizeof(HistorySample) + 96U * 1024U) {
      samples = static_cast<HistorySample*>(heap_caps_malloc(
          capacity * sizeof(HistorySample), MALLOC_CAP_8BIT));
    }
    if (samples == nullptr) {
      sendJsonResult(false, "History is temporarily unavailable");
      return;
    }
  }
  const size_t count = registry_->history(mac, samples, capacity);
  const uint32_t bucketSeconds = registry_->historyBucketSeconds(mac);
  sendNoCache(server_);
  server_.setContentLength(CONTENT_LENGTH_UNKNOWN);
  server_.send(200, "application/json", "");
  String opening = "{\"mac\":\"" + SensorRegistry::formatMac(mac) +
                   "\",\"bucketSeconds\":" + String(bucketSeconds) +
                   ",\"bucketMinutes\":" +
                   String(bucketSeconds / 60.0F, 2) + ",\"points\":[";
  server_.sendContent(opening);
  String chunk;
  chunk.reserve(2048);
  size_t emitted = 0;
  for (size_t i = 0; i < count; ++i) {
    const HistorySample& sample = samples[i];
    if (sample.timestamp < since) continue;
    String point = emitted++ == 0 ? "{" : ",{";
    point.reserve(256);
    point += "\"t\":";
    point += String(static_cast<unsigned long long>(sample.timestamp) *
                    1000ULL);
    point += ",\"sensorType\":";
    point += String(sample.sensorType);
    point += ",\"pcbVersion\":";
    point += String(sample.pcbVersion);
    point += ",\"iaqAccuracy\":";
    point += String(sample.iaqAccuracy);
    if ((sample.capabilities & lil::protocol::kMotion) != 0) {
      const char* keys[] = {"ax", "ay", "az", "gx", "gy", "gz"};
      for (size_t axis = 0; axis < 6; ++axis) {
        point += ",\""; point += keys[axis]; point += "\":";
        point += String(axis < 3 ? sample.accelerationMilliG[axis] / 1000.0F :
                        sample.angularRateDeciDps[axis - 3] / 10.0F, 3);
      }
      point += ",\"peakAcceleration\":"; point += String(sample.peakAccelerationMilliG / 1000.0F, 3);
      point += ",\"peakAngularRate\":"; point += String(sample.peakAngularRateDeciDps / 10.0F, 1);
      point += ",\"motionOverrun\":"; point += sample.motionOverrun ? "true" : "false";
    }
    if ((sample.capabilities & lil::protocol::kTemperature) != 0) {
      point += ",\"temperature\":";
      point += String(sample.temperatureCentiC / 100.0F, 2);
    }
    if ((sample.capabilities & lil::protocol::kHumidity) != 0) {
      point += ",\"humidity\":";
      point += String(sample.humidityCentiPercent / 100.0F, 2);
    }
    if ((sample.capabilities & lil::protocol::kPressure) != 0) {
      point += ",\"pressure\":";
      point += String(sample.pressureDeciHpa / 10.0F, 1);
    }
    if ((sample.capabilities & lil::protocol::kIaq) != 0 &&
        sample.iaqAccuracy > 0) {
      point += ",\"iaq\":";
      point += String(sample.iaqDeci / 10.0F, 1);
    }
    if ((sample.capabilities & lil::protocol::kGasResistance) != 0) {
      point += ",\"gas\":";
      point += String(sample.gasResistanceOhms / 1000.0F, 3);
    }
    if ((sample.capabilities & lil::protocol::kBattery) != 0) {
      point += ",\"battery\":";
      point += String(sample.batteryMillivolts / 1000.0F, 3);
    }
    point += '}';
    if (chunk.length() + point.length() > 2048) {
      server_.sendContent(chunk);
      chunk = String();
      chunk.reserve(2048);
    }
    chunk += point;
  }
  if (!chunk.isEmpty()) {
    server_.sendContent(chunk);
  }
  server_.sendContent("]}");
  server_.sendContent("");
  server_.setContentLength(CONTENT_LENGTH_NOT_SET);
  if (samples != nullptr) {
    heap_caps_free(samples);
  }
}

void WebPortal::sendJsonConfig() {
  JsonDocument document;
  document["storageAvailable"] = store_->storageAvailable();
  document["hostname"] = "w-charger";
  document["wifiSsid"] = config_->wifiSsid;
  document["wifiPasswordSet"] = config_->wifiPassword[0] != '\0';
  document["adminPasswordSet"] = authenticationEnabled();
  document["userApiKey"] = config_->thingSpeakUserApiKey;
  document["defaultSleepSeconds"] = config_->defaultSleepSeconds;
  document["fallbackChannel"] = config_->fallbackWifiChannel;
  document["apActive"] = wifi_->setupPortalActive();
  document["apSsid"] = wifi_->accessPointSsid();
  document["apIp"] = wifi_->accessPointIp();
  document["accessPointPassword"] = config_->accessPointPassword;
  document["csrfToken"] = csrfToken_;
  JsonArray channels = document["thingSpeakChannels"].to<JsonArray>();
  for (size_t i = 0; i < kMaxThingSpeakChannels; ++i) {
    const auto& profile = config_->thingSpeakChannels[i];
    if (!profile.occupied) {
      continue;
    }
    JsonObject item = channels.add<JsonObject>();
    item["slot"] = i;
    item["name"] = profile.name;
    item["channelId"] = profile.channelId;
    item["readApiKey"] = profile.readApiKey;
    item["writeApiKey"] = profile.writeApiKey;
  }
  String output;
  serializeJson(document, output);
  sendNoCache(server_);
  server_.send(200, "application/json", output);
}

void WebPortal::sendWifiScan() {
  if (server_.arg("refresh") == "1") {
    wifi_->requestNetworkScan();
  }
  WifiNetwork networks[kMaxScannedNetworks];
  const size_t count =
      wifi_->cachedNetworks(networks, kMaxScannedNetworks);
  JsonDocument document;
  document["scanning"] = wifi_->networkScanInProgress();
  JsonArray items = document["networks"].to<JsonArray>();
  for (size_t i = 0; i < count; ++i) {
    JsonObject item = items.add<JsonObject>();
    item["ssid"] = networks[i].ssid;
    item["rssi"] = networks[i].rssi;
    item["channel"] = networks[i].channel;
    item["secure"] = networks[i].secure;
  }
  String output;
  serializeJson(document, output);
  sendNoCache(server_);
  server_.send(200, "application/json", output);
}

void WebPortal::saveSetup() {
  if (config_->wifiSsid[0] != '\0') {
    sendJsonResult(false,
                   "The station is already configured. Use Settings.");
    return;
  }
  const StationConfig previousConfig = *config_;
  const String oldSsid = config_->wifiSsid;
  const String ssid = server_.arg("ssid");
  const String password = server_.arg("wifiPassword");
  const String userApiKey = server_.arg("userApiKey");
  const String adminPassword = server_.arg("adminPassword");
  const String confirmAdminPassword = server_.arg("confirmAdminPassword");
  uint32_t defaultSleep = 0;
  if (!readUnsignedArgument(server_, "defaultSleep", defaultSleep,
                            kMinSleepSeconds, kMaxSleepSeconds)) {
    sendJsonResult(false, "Invalid measurement interval"); return;
  }
  if ((!adminPassword.isEmpty() &&
       (adminPassword.length() < 8 || adminPassword.length() > 64)) ||
      adminPassword != confirmAdminPassword) {
    sendJsonResult(false,
                   "The website passwords must match and contain 8 to 64 characters.");
    return;
  }
  if (ssid.isEmpty() || ssid.length() > 32 || password.length() > 64 ||
      userApiKey.length() > 40 || defaultSleep < kMinSleepSeconds ||
      defaultSleep > kMaxSleepSeconds) {
    sendJsonResult(false, "Check Wi-Fi and the measurement interval.");
    return;
  }

  copyText(config_->hostname, "w-charger");
  copyText(config_->wifiSsid, ssid);
  if (!password.isEmpty() || ssid != oldSsid) {
    copyText(config_->wifiPassword, password);
  }
  copyText(config_->thingSpeakUserApiKey, userApiKey);
  setAdminPassword(adminPassword);
  config_->defaultSleepSeconds = defaultSleep;
  // Keep the setup portal alive through this reboot.  WifiService clears it
  // and persists completion only after the home WLAN really connects.
  config_->setupPortalRequired = true;
  const bool saved = store_->saveStationConfig(*config_);
  if (!saved) {
    *config_ = previousConfig;
  }
  sendJsonResult(saved,
                 saved ? "Setup saved. W-Charger is restarting."
                       : "Setup could not be saved.",
                 saved);
}

void WebPortal::saveSetupSensor() {
  uint8_t mac[6];
  SensorView view{};
  const String name = server_.arg("name");
  uint32_t sleepSeconds = 0, sensorTypeValue = 0;
  if (!readUnsignedArgument(server_, "sleepSeconds", sleepSeconds,
                            kMinSleepSeconds, kMaxSleepSeconds) ||
      !readUnsignedArgument(server_, "sensorType", sensorTypeValue, 0, 255)) {
    sendJsonResult(false, "Invalid sensor type or interval"); return;
  }
  const auto sensorType =
      static_cast<lil::protocol::EnvironmentalSensorType>(sensorTypeValue);
  const bool validSensorType =
      sensorType == lil::protocol::EnvironmentalSensorType::kAutoDetect ||
      sensorType == lil::protocol::EnvironmentalSensorType::kBme280 ||
      sensorType == lil::protocol::EnvironmentalSensorType::kLsm6dsox ||
      sensorType == lil::protocol::EnvironmentalSensorType::kTmp117 ||
      sensorType == lil::protocol::EnvironmentalSensorType::kMax30102 ||
      sensorType == lil::protocol::EnvironmentalSensorType::kBme680 ||
      sensorType == lil::protocol::EnvironmentalSensorType::kDisabled;
  if (!wifi_->setupPortalActive() ||
      !SensorRegistry::parseMac(server_.arg("mac"), mac) ||
      !registry_->findView(mac, view) || view.config.provisioned) {
    sendJsonResult(false,
                   "The sensor could not be configured. Check the selection and connection.");
    return;
  }
  const bool bme680 =
      sensorType == lil::protocol::EnvironmentalSensorType::kBme680 ||
      (sensorType == lil::protocol::EnvironmentalSensorType::kAutoDetect &&
       view.runtime.telemetry.sensorType ==
           lil::protocol::EnvironmentalSensorType::kBme680);
  if (name.isEmpty() || name.length() > 24 || !validSensorType ||
      sleepSeconds < kMinSleepSeconds || sleepSeconds > kMaxSleepSeconds ||
      (bme680 && (sleepSeconds < 300 || sleepSeconds % 300 != 0))) {
    sendJsonResult(false,
                   "Sensor name, sensor type or interval is invalid.");
    return;
  }

  ThingSpeakFieldMapping fields{};
  if (bme680) {
    fields.iaq = 4;
    fields.gasResistance = 5;
    fields.battery = 6;
  } else if (sensorType == lil::protocol::EnvironmentalSensorType::kBme280) {
    fields.battery = 4;
  }
  const bool saved = registry_->updateConfig(
      mac, name, sleepSeconds, 0, String(), false, fields, 0xFF, sensorType,
      view.config.temperatureOffsetC, view.config.batteryCalibrationFactor);
  sendJsonResult(saved,
                 saved ? "Sensor added. Cloud settings and calibration can be completed later in the dashboard."
                       : "Sensor could not be saved.");
}

void WebPortal::saveStation() {
  const StationConfig previousConfig = *config_;
  const String oldSsid = config_->wifiSsid;
  const String oldApPassword = config_->accessPointPassword;
  const String oldAdminPasswordHash = config_->adminPassword;
  const uint32_t oldDefaultSleep = config_->defaultSleepSeconds;
  const uint8_t oldFallbackChannel = config_->fallbackWifiChannel;
  const String ssid = server_.arg("ssid");
  const String wifiPassword = server_.arg("wifiPassword");
  const String apPassword = server_.arg("apPassword");
  const String userApiKey = server_.arg("userApiKey");
  const String newAdminPassword = server_.arg("newAdminPassword");
  const String confirmAdminPassword = server_.arg("confirmAdminPassword");
  const bool removeAdminPassword = server_.hasArg("removeAdminPassword");
  uint32_t defaultSleep = 0, fallbackChannelValue = 0;
  if (!readUnsignedArgument(server_, "defaultSleep", defaultSleep,
                            kMinSleepSeconds, kMaxSleepSeconds) ||
      !readUnsignedArgument(server_, "fallbackChannel", fallbackChannelValue, 1, 13)) {
    sendJsonResult(false, "Invalid station interval or radio channel"); return;
  }
  if (ssid.isEmpty() || ssid.length() > 32 || wifiPassword.length() > 64 ||
      userApiKey.length() > 40 || defaultSleep < kMinSleepSeconds ||
      defaultSleep > kMaxSleepSeconds || fallbackChannelValue < 1 ||
      fallbackChannelValue > 13 ||
      (!apPassword.isEmpty() &&
       (apPassword.length() < 8 || apPassword.length() > 63)) ||
      (!newAdminPassword.isEmpty() &&
       (newAdminPassword.length() < 8 || newAdminPassword.length() > 64)) ||
      newAdminPassword != confirmAdminPassword ||
      (removeAdminPassword && !newAdminPassword.isEmpty())) {
    sendJsonResult(false, "Invalid station configuration");
    return;
  }
  const uint8_t fallbackChannel =
      static_cast<uint8_t>(fallbackChannelValue);

  copyText(config_->hostname, "w-charger");
  copyText(config_->wifiSsid, ssid);
  if (!wifiPassword.isEmpty() || ssid != oldSsid) {
    copyText(config_->wifiPassword, wifiPassword);
  }
  if (!apPassword.isEmpty()) {
    copyText(config_->accessPointPassword, apPassword);
  }
  copyText(config_->thingSpeakUserApiKey, userApiKey);
  if (removeAdminPassword) {
    setAdminPassword(String());
  } else if (!newAdminPassword.isEmpty()) {
    setAdminPassword(newAdminPassword);
  }
  config_->defaultSleepSeconds = defaultSleep;
  config_->fallbackWifiChannel = fallbackChannel;
  const bool saved = store_->saveStationConfig(*config_);
  const bool authenticationChanged =
      saved && oldAdminPasswordHash != config_->adminPassword;
  if (!saved) {
    *config_ = previousConfig;
  }
  const bool restartRequested = server_.arg("restartNow") == "1";
  const bool restartRequired =
      saved && (ssid != oldSsid || !wifiPassword.isEmpty() ||
                (!apPassword.isEmpty() && apPassword != oldApPassword) ||
                defaultSleep != oldDefaultSleep ||
                fallbackChannel != oldFallbackChannel || restartRequested);
  if (authenticationChanged) {
    clearAuthSessions();
    refreshCsrfToken();
    server_.sendHeader(
        "Set-Cookie",
        String(kSessionCookieName) +
            "=; Path=/; Max-Age=0; HttpOnly; SameSite=Strict");
  }
  sendJsonResult(saved,
                 saved ? (restartRequired
                              ? "Network or measurement settings saved. W-Charger is restarting."
                              : "Settings saved and applied.")
                       : "Save failed",
                 restartRequired, authenticationChanged);
}

void WebPortal::saveSensor() {
  uint8_t mac[6];
  uint32_t sleepSeconds = 0, channelId = 0, sensorTypeValue = 0;
  if (!readUnsignedArgument(server_, "sleepSeconds", sleepSeconds,
                            kMinSleepSeconds, kMaxSleepSeconds) ||
      !readUnsignedArgument(server_, "channelId", channelId, 0, UINT32_MAX, true) ||
      !readUnsignedArgument(server_, "sensorType", sensorTypeValue, 0, 255)) {
    sendJsonResult(false, "Invalid sensor configuration"); return;
  }
  String writeKey = server_.arg("writeKey");
  int profileIndex = -1;
  if (server_.hasArg("profileSlot") && server_.arg("profileSlot") != "-1") {
    uint32_t parsedSlot = 0;
    if (!readUnsignedArgument(server_, "profileSlot", parsedSlot, 0,
                              kMaxThingSpeakChannels - 1) ||
        !config_->thingSpeakChannels[parsedSlot].occupied) {
      sendJsonResult(false, "Invalid channel profile"); return;
    }
    profileIndex = static_cast<int>(parsedSlot);
  }
  uint8_t profileSlot = 0xFF;
  if (profileIndex >= 0 &&
      profileIndex < static_cast<int>(kMaxThingSpeakChannels) &&
      config_->thingSpeakChannels[profileIndex].occupied) {
    const auto& profile = config_->thingSpeakChannels[profileIndex];
    profileSlot = static_cast<uint8_t>(profileIndex);
    channelId = profile.channelId;
    writeKey = profile.writeApiKey;
  }
  const bool uploadEnabled = server_.hasArg("uploadEnabled");
  ThingSpeakFieldMapping fields{};
  if (!readFieldArgument(server_, "temperatureField", fields.temperature) ||
      !readFieldArgument(server_, "humidityField", fields.humidity) ||
      !readFieldArgument(server_, "pressureField", fields.pressure) ||
      !readFieldArgument(server_, "iaqField", fields.iaq) ||
      !readFieldArgument(server_, "batteryField", fields.battery) ||
      !readFieldArgument(server_, "gasResistanceField", fields.gasResistance)) {
    sendJsonResult(false, "ThingSpeak fields must be integers from 0 to 8"); return;
  }
  const auto sensorType =
      static_cast<lil::protocol::EnvironmentalSensorType>(sensorTypeValue);
  float temperatureOffsetC = 0;
  if (server_.hasArg("temperatureOffsetC") &&
      !webinput::finiteDecimal(server_.arg("temperatureOffsetC").c_str(),
                               temperatureOffsetC, -10.0F, 10.0F)) {
    sendJsonResult(false, "Invalid temperature offset"); return;
  }
  const bool validSensorType =
      sensorType == lil::protocol::EnvironmentalSensorType::kAutoDetect ||
      sensorType == lil::protocol::EnvironmentalSensorType::kBme280 ||
      sensorType == lil::protocol::EnvironmentalSensorType::kLsm6dsox ||
      sensorType == lil::protocol::EnvironmentalSensorType::kTmp117 ||
      sensorType == lil::protocol::EnvironmentalSensorType::kMax30102 ||
      sensorType == lil::protocol::EnvironmentalSensorType::kBme680 ||
      sensorType == lil::protocol::EnvironmentalSensorType::kDisabled;
  SensorView existingView{};
  if (!SensorRegistry::parseMac(server_.arg("mac"), mac) ||
      !registry_->findView(mac, existingView) ||
      server_.arg("name").isEmpty() || server_.arg("name").length() > 24 ||
      sleepSeconds < kMinSleepSeconds || sleepSeconds > kMaxSleepSeconds ||
      writeKey.length() > 32 || !validSensorType ||
      !isfinite(temperatureOffsetC) || temperatureOffsetC < -10.0F ||
      temperatureOffsetC > 10.0F ||
      (sensorType == lil::protocol::EnvironmentalSensorType::kBme680 &&
       (sleepSeconds < 300 || sleepSeconds % 300 != 0))) {
    sendJsonResult(false, "Invalid sensor configuration");
    return;
  }
  const SensorConfig& existing = existingView.config;
  const bool bme680Effective =
      sensorType == lil::protocol::EnvironmentalSensorType::kBme680 ||
      (sensorType == lil::protocol::EnvironmentalSensorType::kAutoDetect &&
       existingView.runtime.telemetry.sensorType ==
           lil::protocol::EnvironmentalSensorType::kBme680);
  if (bme680Effective && (sleepSeconds < 300 || sleepSeconds % 300 != 0)) {
    sendJsonResult(
        false,
        "A detected BME680 requires a five-minute interval or a multiple of five minutes.");
    return;
  }
  float batteryCalibrationFactor = existing.batteryCalibrationFactor;
  if (server_.hasArg("resetBatteryCalibration")) {
    batteryCalibrationFactor = 1.0F;
  } else {
    const String batteryReference = server_.arg("batteryReferenceVoltage");
    if (!batteryReference.isEmpty()) {
      char* end = nullptr;
      const float referenceVoltage = strtof(batteryReference.c_str(), &end);
      const uint16_t measuredMillivolts =
          existingView.runtime.telemetry.batteryMillivolts;
      if (end == batteryReference.c_str() ||
          *end != '\0' || !isfinite(referenceVoltage) ||
          referenceVoltage < 2.0F || referenceVoltage > 5.0F ||
          !existingView.runtime.hasTelemetry || measuredMillivolts < 2000 ||
          (existingView.runtime.telemetry.flags &
           lil::protocol::kBatteryReadFailed) != 0) {
        sendJsonResult(
            false,
            "Battery calibration failed. Check the reference voltage and latest measurement.");
        return;
      }
      batteryCalibrationFactor *=
          referenceVoltage * 1000.0F / measuredMillivolts;
      if (!isfinite(batteryCalibrationFactor) ||
          batteryCalibrationFactor < 0.7F ||
          batteryCalibrationFactor > 1.3F) {
        sendJsonResult(
            false,
            "The calculated correction factor is implausible. Check the PCB version, voltage divider and multimeter value.");
        return;
      }
    }
  }
  if (!validThingSpeakFields(fields, uploadEnabled)) {
    sendJsonResult(
        false,
        "Do not assign ThingSpeak fields 1-8 more than once. At least "
        "one measurement must be enabled.");
    return;
  }
  const bool storedKeyUsable = profileSlot == 0xFF &&
                               channelId == existing.thingSpeakChannelId &&
                               existing.thingSpeakWriteKey[0] != '\0';
  if (writeKey.isEmpty() && storedKeyUsable) {
    writeKey = existing.thingSpeakWriteKey;
  }
  if (uploadEnabled &&
      (channelId == 0 || writeKey.isEmpty())) {
    sendJsonResult(false,
                   "Cloud upload requires a Channel ID and Write API Key.");
    return;
  }
  const bool saved = registry_->updateConfig(
      mac, server_.arg("name"), sleepSeconds, channelId, writeKey,
      uploadEnabled, fields, profileSlot, sensorType, temperatureOffsetC,
      batteryCalibrationFactor);
  sendJsonResult(saved,
                 saved ? "Sensor settings will be sent at the next check-in."
                       : "Sensor not found");
}

void WebPortal::saveChannelProfile() {
  const StationConfig previousConfig = *config_;
  uint32_t requestedSlot = 0;
  if (server_.hasArg("slot") &&
      !readUnsignedArgument(server_, "slot", requestedSlot, 0, kMaxThingSpeakChannels - 1)) {
    sendJsonResult(false, "Invalid channel profile"); return;
  }
  int slot = server_.hasArg("slot") ? static_cast<int>(requestedSlot) : -1;
  if (slot < 0) {
    slot = -1;
    for (size_t i = 0; i < kMaxThingSpeakChannels; ++i) {
      if (!config_->thingSpeakChannels[i].occupied) {
        slot = static_cast<int>(i);
        break;
      }
    }
  }
  const String name = server_.arg("name");
  uint32_t channelId = 0;
  if (!readUnsignedArgument(server_, "channelId", channelId, 1)) {
    sendJsonResult(false, "Invalid Channel ID"); return;
  }
  const String readApiKey = server_.arg("readApiKey");
  const String writeApiKey = server_.arg("writeApiKey");
  if (slot < 0 || channelId == 0 || name.length() > 24 ||
      readApiKey.length() > 32 || writeApiKey.length() > 32) {
    sendJsonResult(false,
                   slot < 0 ? "A maximum of six channels is supported."
                            : "Check the Channel ID and API keys.");
    return;
  }
  auto& profile = config_->thingSpeakChannels[slot];
  profile = ThingSpeakChannelProfile{};
  profile.occupied = true;
  copyText(profile.name,
           name.isEmpty() ? "Channel " + String(channelId) : name);
  profile.channelId = channelId;
  copyText(profile.readApiKey, readApiKey);
  copyText(profile.writeApiKey, writeApiKey);
  if (slot == 0) {
    config_->thingSpeakDefaultChannelId = channelId;
    copyText(config_->thingSpeakReadApiKey, readApiKey);
    copyText(config_->thingSpeakWriteApiKey, writeApiKey);
  }
  const bool stationSaved = store_->saveStationConfig(*config_);
  const bool saved = stationSaved && registry_->syncThingSpeakProfile(slot, profile);
  if (!saved) {
    *config_ = previousConfig;
    if (stationSaved) store_->saveStationConfig(previousConfig);
  }
  sendJsonResult(saved, saved ? "ThingSpeak channel saved."
                               : "Channel could not be saved.");
}

void WebPortal::deleteChannelProfile() {
  const StationConfig previousConfig = *config_;
  uint32_t slot = 0;
  if (!readUnsignedArgument(server_, "slot", slot, 0, kMaxThingSpeakChannels - 1) ||
      !config_->thingSpeakChannels[slot].occupied) {
    sendJsonResult(false, "Channel not found.");
    return;
  }
  config_->thingSpeakChannels[slot] = ThingSpeakChannelProfile{};
  if (slot == 0) {
    config_->thingSpeakDefaultChannelId = 0;
    config_->thingSpeakReadApiKey[0] = '\0';
    config_->thingSpeakWriteApiKey[0] = '\0';
  }
  const bool stationSaved = store_->saveStationConfig(*config_);
  const bool saved = stationSaved && registry_->removeThingSpeakProfile(slot);
  if (!saved) {
    *config_ = previousConfig;
    if (stationSaved) store_->saveStationConfig(previousConfig);
  }
  sendJsonResult(saved, saved ? "ThingSpeak channel removed."
                               : "Channel could not be removed.");
}

void WebPortal::createThingSpeakChannel() {
  uint8_t mac[6];
  SensorConfig sensor{};
  if (!SensorRegistry::parseMac(server_.arg("mac"), mac) ||
      !registry_->findConfig(mac, sensor)) {
    sendJsonResult(false, "Sensor not found");
    return;
  }
  const String requestedName = server_.arg("name");
  if (requestedName.length() > 24) {
    sendJsonResult(false, "The sensor name is too long.");
    return;
  }
  const String channelName = requestedName.isEmpty()
                                 ? String(sensor.name)
                                 : requestedName;
  int profileSlot = -1;
  for (size_t i = 0; i < kMaxThingSpeakChannels; ++i) {
    if (!config_->thingSpeakChannels[i].occupied) {
      profileSlot = static_cast<int>(i);
      break;
    }
  }
  if (profileSlot < 0) {
    sendJsonResult(false, "A maximum of six channels is supported.");
    return;
  }
  const ChannelCreationResult result = thingSpeak_->createChannel(
      config_->thingSpeakUserApiKey, channelName);
  if (!result.success) {
    sendJsonResult(false, result.error);
    return;
  }
  const StationConfig previousConfig = *config_;
  auto& profile = config_->thingSpeakChannels[profileSlot];
  profile.occupied = true;
  copyText(profile.name, channelName);
  profile.channelId = result.channelId;
  copyText(profile.readApiKey, result.readKey);
  copyText(profile.writeApiKey, result.writeKey);
  if (profileSlot == 0) {
    config_->thingSpeakDefaultChannelId = result.channelId;
    copyText(config_->thingSpeakReadApiKey, result.readKey);
    copyText(config_->thingSpeakWriteApiKey, result.writeKey);
  }
  if (!store_->saveStationConfig(*config_)) {
    *config_ = previousConfig;
    sendJsonResult(false,
                   "ThingSpeak channel " + String(result.channelId) +
                   " was created, but its local profile could not be saved. Reload account channels before retrying.");
    return;
  }

  JsonDocument document;
  document["success"] = true;
  document["message"] = "ThingSpeak-Channel " + String(result.channelId) +
                        " was created. Assign its fields next.";
  document["restart"] = false;
  document["slot"] = profileSlot;
  document["channelId"] = result.channelId;
  String output;
  serializeJson(document, output);
  sendNoCache(server_);
  server_.send(200, "application/json", output);
}

void WebPortal::listThingSpeakChannels() {
  const ThingSpeakApiResult result =
      thingSpeak_->listChannels(config_->thingSpeakUserApiKey);
  if (!result.success) {
    sendJsonResult(false, result.error);
    return;
  }

  JsonDocument remote;
  if (deserializeJson(remote, result.response) ||
      !remote.is<JsonArray>()) {
    sendJsonResult(false, "ThingSpeak returned an invalid channel list.");
    return;
  }

  JsonDocument document;
  document["success"] = true;
  document["message"] = "ThingSpeak channels loaded.";
  JsonArray channels = document["channels"].to<JsonArray>();
  for (JsonObjectConst source : remote.as<JsonArrayConst>()) {
    const uint32_t channelId = source["id"] | 0U;
    if (channelId == 0) {
      continue;
    }
    String readKey;
    String writeKey;
    extractApiKeys(source, readKey, writeKey);
    int localSlot = -1;
    for (size_t slot = 0; slot < kMaxThingSpeakChannels; ++slot) {
      if (config_->thingSpeakChannels[slot].occupied &&
          config_->thingSpeakChannels[slot].channelId == channelId) {
        localSlot = static_cast<int>(slot);
        if (readKey.isEmpty()) {
          readKey = config_->thingSpeakChannels[slot].readApiKey;
        }
        if (writeKey.isEmpty()) {
          writeKey = config_->thingSpeakChannels[slot].writeApiKey;
        }
        break;
      }
    }
    JsonObject item = channels.add<JsonObject>();
    item["id"] = channelId;
    item["name"] = source["name"] | "Unnamed channel";
    item["description"] = source["description"] | "";
    item["metadata"] = source["metadata"] | "";
    item["tags"] = tagsAsText(source["tags"]);
    item["url"] = source["url"] | "";
    item["latitude"] = source["latitude"] | "";
    item["longitude"] = source["longitude"] | "";
    item["elevation"] = source["elevation"] | "";
    item["publicFlag"] = source["public_flag"] | false;
    item["lastEntryId"] = source["last_entry_id"] | 0U;
    item["createdAt"] = source["created_at"] | "";
    item["updatedAt"] = source["updated_at"] | "";
    item["readApiKey"] = readKey;
    item["writeApiKey"] = writeKey;
    item["localSlot"] = localSlot;
    item["channelUrl"] =
        "https://thingspeak.com/channels/" + String(channelId);
    item["privateUrl"] = "https://thingspeak.com/channels/" +
                         String(channelId) + "/private_show";
    item["feedUrl"] = "https://api.thingspeak.com/channels/" +
                      String(channelId) + "/feeds.json";
    JsonArray fields = item["fields"].to<JsonArray>();
    for (uint8_t field = 1; field <= 8; ++field) {
      fields.add(source["field" + String(field)] | "");
    }
  }
  String output;
  serializeJson(document, output);
  sendNoCache(server_);
  server_.send(200, "application/json", output);
}

void WebPortal::createManagedThingSpeakChannel() {
  if (!validManagedChannelRequest(server_)) {
    sendJsonResult(false, "Check the name and channel fields.");
    return;
  }
  const ThingSpeakApiResult result = thingSpeak_->createManagedChannel(
      config_->thingSpeakUserApiKey, managedChannelSettings(server_));
  if (!result.success) {
    sendJsonResult(false, result.error);
    return;
  }
  JsonDocument remote;
  if (deserializeJson(remote, result.response)) {
    sendJsonResult(false, "Channel created, but the response was invalid.");
    return;
  }
  const uint32_t channelId = remote["id"] | 0U;
  if (!channelId) {
    sendJsonResult(false,
                   "The cloud response contained no Channel ID. Reload account channels before retrying.");
    return;
  }
  const StationConfig previousConfig = *config_;
  String readKey;
  String writeKey;
  extractApiKeys(remote.as<JsonObjectConst>(), readKey, writeKey);
  int localSlot = -1;
  for (size_t slot = 0; slot < kMaxThingSpeakChannels; ++slot) {
    if (!config_->thingSpeakChannels[slot].occupied) {
      localSlot = static_cast<int>(slot);
      break;
    }
  }
  if (localSlot >= 0 && channelId != 0) {
    auto& profile = config_->thingSpeakChannels[localSlot];
    profile.occupied = true;
    copyText(profile.name, server_.arg("name"));
    profile.channelId = channelId;
    copyText(profile.readApiKey, readKey);
    copyText(profile.writeApiKey, writeKey);
    if (localSlot == 0) {
      config_->thingSpeakDefaultChannelId = channelId;
      copyText(config_->thingSpeakReadApiKey, readKey);
      copyText(config_->thingSpeakWriteApiKey, writeKey);
    }
    if (!store_->saveStationConfig(*config_)) {
      *config_ = previousConfig;
      sendJsonResult(false,
                     "ThingSpeak channel " + String(channelId) +
                     " was created, but its local profile could not be saved. Reload account channels before retrying.");
      return;
    }
  }
  JsonDocument document;
  document["success"] = channelId != 0;
  document["restart"] = false;
  document["message"] = localSlot >= 0
                            ? "ThingSpeak channel created and imported locally."
                            : "ThingSpeak channel created. The local profile list is full.";
  document["channelId"] = channelId;
  document["slot"] = localSlot;
  String output;
  serializeJson(document, output);
  sendNoCache(server_);
  server_.send(channelId != 0 ? 200 : 400, "application/json", output);
}

void WebPortal::updateManagedThingSpeakChannel() {
  uint32_t channelId = 0;
  if (!readUnsignedArgument(server_, "channelId", channelId, 1)) {
    sendJsonResult(false, "Invalid Channel ID"); return;
  }
  if (channelId == 0 || !validManagedChannelRequest(server_)) {
    sendJsonResult(false, "Check the Channel ID, name and fields.");
    return;
  }
  const ThingSpeakApiResult result = thingSpeak_->updateChannel(
      config_->thingSpeakUserApiKey, channelId,
      managedChannelSettings(server_));
  if (!result.success) {
    sendJsonResult(false, result.error);
    return;
  }
  JsonDocument remote;
  String readKey;
  String writeKey;
  if (!deserializeJson(remote, result.response)) {
    extractApiKeys(remote.as<JsonObjectConst>(), readKey, writeKey);
  }
  const StationConfig previousConfig = *config_;
  bool changed[kMaxThingSpeakChannels]{};
  bool localChanged = false;
  for (size_t slot = 0; slot < kMaxThingSpeakChannels; ++slot) {
    auto& profile = config_->thingSpeakChannels[slot];
    if (!profile.occupied || profile.channelId != channelId) continue;
    copyText(profile.name, server_.arg("name"));
    if (!readKey.isEmpty()) copyText(profile.readApiKey, readKey);
    if (!writeKey.isEmpty()) copyText(profile.writeApiKey, writeKey);
    if (slot == 0) {
      config_->thingSpeakDefaultChannelId = profile.channelId;
      copyText(config_->thingSpeakReadApiKey, profile.readApiKey);
      copyText(config_->thingSpeakWriteApiKey, profile.writeApiKey);
    }
    changed[slot] = true;
    localChanged = true;
  }
  // Save the station profile before applying it to live sensor assignments.
  // A successful cloud mutation remains successful even if this local save
  // fails; only local state can be restored here.
  const bool stationSaved = !localChanged || store_->saveStationConfig(*config_);
  bool localSaved = stationSaved;
  if (stationSaved && localChanged) {
    for (size_t slot = 0; slot < kMaxThingSpeakChannels; ++slot) if (changed[slot]) {
      localSaved = registry_->syncThingSpeakProfile(slot, config_->thingSpeakChannels[slot]) && localSaved;
    }
  }
  if (!localSaved) {
    *config_ = previousConfig;
    if (stationSaved) {
      // Rollback is best effort when NVS remains unavailable. Registry helpers
      // also retain pending persistence so restored assignments can retry.
      store_->saveStationConfig(previousConfig);
      for (size_t slot = 0; slot < kMaxThingSpeakChannels; ++slot) if (changed[slot])
        registry_->syncThingSpeakProfile(slot, previousConfig.thingSpeakChannels[slot]);
    }
  }
  sendJsonResult(localSaved,
                 localSaved ? "ThingSpeak channel updated."
                            : "Cloud updated, but the local assignment could not be saved.");
}

void WebPortal::clearManagedThingSpeakChannel() {
  uint32_t channelId = 0;
  if (!readUnsignedArgument(server_, "channelId", channelId, 1)) {
    sendJsonResult(false, "Invalid Channel ID"); return;
  }
  if (channelId == 0) {
    sendJsonResult(false, "Invalid Channel ID.");
    return;
  }
  const ThingSpeakApiResult result = thingSpeak_->clearChannel(
      config_->thingSpeakUserApiKey, channelId);
  sendJsonResult(result.success,
                 result.success ? "All channel measurements were cleared."
                                : result.error);
}

void WebPortal::deleteManagedThingSpeakChannel() {
  uint32_t channelId = 0;
  if (!readUnsignedArgument(server_, "channelId", channelId, 1)) {
    sendJsonResult(false, "Invalid Channel ID"); return;
  }
  if (channelId == 0) {
    sendJsonResult(false, "Invalid Channel ID.");
    return;
  }
  const ThingSpeakApiResult result = thingSpeak_->deleteChannel(
      config_->thingSpeakUserApiKey, channelId);
  if (!result.success) {
    sendJsonResult(false, result.error);
    return;
  }
  bool saved = true;
  bool changed = false;
  for (size_t slot = 0; slot < kMaxThingSpeakChannels; ++slot) {
    auto& profile = config_->thingSpeakChannels[slot];
    if (!profile.occupied || profile.channelId != channelId) {
      continue;
    }
    profile = ThingSpeakChannelProfile{};
    if (slot == 0) {
      config_->thingSpeakDefaultChannelId = 0;
      config_->thingSpeakReadApiKey[0] = '\0';
      config_->thingSpeakWriteApiKey[0] = '\0';
    }
    changed = true;
    saved = registry_->removeThingSpeakProfile(slot) && saved;
  }
  if (changed) {
    saved = store_->saveStationConfig(*config_) && saved;
  }
  sendJsonResult(saved,
                 saved ? "ThingSpeak channel and local assignment deleted."
                       : "Cloud channel deleted, but the local assignment could not be fully updated.");
}

void WebPortal::resetSensor() {
  uint8_t mac[6];
  const bool ok = SensorRegistry::parseMac(server_.arg("mac"), mac) &&
                  registry_->requestFactoryReset(mac);
  sendJsonResult(ok, ok ? "The sensor will be reset at its next check-in."
                        : "Sensor not found");
}

void WebPortal::resetSensorIaqCalibration() {
  uint8_t mac[6];
  const bool ok = SensorRegistry::parseMac(server_.arg("mac"), mac) &&
                  registry_->requestIaqCalibrationReset(mac);
  sendJsonResult(
      ok,
      ok ? "The IAQ learning state will be cleared at the next check-in, then calibration will restart."
         : "Sensor not found");
}

void WebPortal::deleteSensor() {
  uint8_t mac[6];
  const bool ok = SensorRegistry::parseMac(server_.arg("mac"), mac) &&
                  registry_->deleteSensor(mac);
  if (ok) otaService.forget(mac);
  sendJsonResult(
      ok,
      ok ? "Sensor removed from the station. A powered sensor will be detected again at its next check-in."
         : "Sensor not found");
}

void WebPortal::factoryReset() {
  if (server_.arg("confirm") != "RESET") {
    sendJsonResult(false, "Confirmation does not match");
    return;
  }
  const bool cleared = store_->factoryReset();
  if (cleared) otaService.forget();
  sendJsonResult(cleared,
                 cleared
                     ? "Factory settings cleared. W-Charger is restarting."
                     : "Factory settings could not be cleared.",
                 cleared);
}

void WebPortal::sendJsonResult(bool success, const String& message,
                               bool restartRequired,
                               bool authenticationChanged) {
  JsonDocument document;
  document["success"] = success;
  document["message"] = message;
  document["restart"] = restartRequired;
  document["authenticationChanged"] = authenticationChanged;
  String output;
  serializeJson(document, output);
  sendNoCache(server_);
  server_.send(success ? 200 : 400, "application/json", output);
  if (restartRequired) {
    scheduleRestart();
  }
}

void WebPortal::scheduleRestart() {
  restartAtMs_ = millis() + 2500;
}

}  // namespace station
