Ans1S/esp32-c3-iot-sensor-board/Firmware/shared/src/recording_journal.cpp

#include "recording_journal.h"

namespace lil::recording {
namespace {
constexpr uint32_t kMagic = 0x52454331;
bool erased(const void* data, size_t count) {
  const auto* bytes = static_cast<const uint8_t*>(data);
  for (size_t i = 0; i < count; ++i) if (bytes[i] != 0xff) return false;
  return true;
}
bool bit(const uint8_t* bits, uint8_t slot) { return bits[slot / 8] & (1U << (slot % 8)); }
}
bool Journal::readHeader(size_t page, Header& header) {
  return flash_->read(page * kPageBytes, &header, sizeof(header));
}
bool Journal::clearBit(size_t page, size_t field, uint8_t slot) {
  const size_t offset = page * kPageBytes + field + (slot / 32) * 4;
  uint32_t word;
  if (!flash_->read(offset, &word, 4)) return false;
  word &= ~(1UL << (slot % 32));
  uint32_t check;
  return flash_->write(offset, &word, 4) && flash_->read(offset, &check, 4) && check == word;
}
bool Journal::begin(Flash& flash, uint64_t sessionFilter) {
  flash_ = &flash; fault_ = false; pending_ = generation_ = lastSampleMs_ = 0;
  pages_.assign(flash.bytes() / kPageBytes, {});
  if (pages_.empty()) return false;
  for (size_t page = 0; page < pages_.size(); ++page) {
    Header header;
    auto& state = pages_[page];
    if (!readHeader(page, header)) return false;
    if (erased(&header, sizeof(header))) continue;
    if (header.magic != kMagic || header.version != kFormat ||
        (header.width != 32 && header.width != 64 && header.width != 128) ||
        header.crc != protocol::crc32(reinterpret_cast<const uint8_t*>(&header), 12)) {
      state.usable = false; fault_ = true; continue;
    }
    state.generation = header.generation; state.width = header.width;
    if (state.generation > generation_) generation_ = state.generation;
    const uint8_t slots = (kPageBytes - kHeaderBytes) / state.width;
    bool belongs = false;
    for (uint8_t slot = 0; slot < slots; ++slot) {
      Record record{};
      if (!flash.read(page * kPageBytes + kHeaderBytes + slot * state.width, &record, state.width)) return false;
      if (erased(&record, state.width)) {
        if (!bit(header.committed, slot)) { fault_ = true; state.usable = false; }
        continue;
      }
      state.next = slot + 1; // Torn writes burn a slot, never overwrite it.
      if (sessionFilter && record.session != sessionFilter) continue;
      belongs = true;
      if (valid(record) && record.sampleMs > lastSampleMs_) lastSampleMs_ = record.sampleMs;
      if (bit(header.committed, slot) && size(record.type) == state.width && valid(record)) {
        if (!clearBit(page, offsetof(Header, committed), slot)) return false;
        header.committed[slot / 8] &= ~(1U << (slot % 8));
      }
      if (!bit(header.committed, slot) && bit(header.acknowledged, slot)) {
        ++state.pending; ++pending_;
        if (size(record.type) != state.width || !valid(record)) fault_ = true;
      }
    }
    // A new user-started session logically replaces the old one. Erase pages
    // lazily as needed, not all 1.375 MiB before the first measurement.
    if (sessionFilter && !belongs && state.usable) state = {};
  }
  return true;
}
bool Journal::clear() {
  if (!flash_) return false;
  for (size_t page = 0; page < pages_.size(); ++page)
    if (!flash_->erase(page * kPageBytes, kPageBytes)) { fault_ = true; return false; }
  return begin(*flash_);
}
bool Journal::initialize(size_t page, size_t width) {
  if (pages_[page].pending || !pages_[page].usable || generation_ == UINT32_MAX) return false;
  if (!flash_->erase(page * kPageBytes, kPageBytes)) { fault_ = true; return false; }
  Header header;
  memset(&header, 0xff, sizeof(header));
  header.magic = kMagic; header.generation = ++generation_;
  header.width = width; header.version = kFormat;
  header.crc = protocol::crc32(reinterpret_cast<const uint8_t*>(&header), 12);
  if (!flash_->write(page * kPageBytes, &header, 16)) { fault_ = true; pages_[page].usable = false; return false; }
  pages_[page] = {}; pages_[page].width = width; pages_[page].generation = generation_;
  return true;
}
bool Journal::append(const Record& record) {
  if (!flash_ || !valid(record)) return false;
  const size_t width = size(record.type);
  size_t chosen = pages_.size();
  uint32_t newest = 0;
  for (size_t i = 0; i < pages_.size(); ++i) {
    const auto& page = pages_[i];
    if (page.usable && page.width == width && page.next < (kPageBytes - kHeaderBytes) / width && page.generation > newest) {
      chosen = i; newest = page.generation;
    }
  }
  if (chosen == pages_.size()) {
    uint32_t oldest = UINT32_MAX;
    for (size_t i = 0; i < pages_.size(); ++i)
      if (pages_[i].usable && !pages_[i].pending && pages_[i].generation < oldest) {
        chosen = i; oldest = pages_[i].generation;
      }
    if (chosen == pages_.size() || !initialize(chosen, width)) return false;
  }
  auto& page = pages_[chosen];
  const uint8_t slot = page.next++;
  const size_t offset = chosen * kPageBytes + kHeaderBytes + slot * width;
  Record check{};
  if (!flash_->write(offset, &record, width) || !flash_->read(offset, &check, width) ||
      memcmp(&record, &check, width) || !clearBit(chosen, offsetof(Header, committed), slot)) {
    // Reopen before further writes: a failed commit may have reached flash.
    page.usable = false; fault_ = true; return false;
  }
  ++page.pending; ++pending_; lastSampleMs_ = record.sampleMs; return true;
}
bool Journal::locate(size_t& page, uint8_t& slot) {
  page = pages_.size(); uint32_t oldest = UINT32_MAX;
  for (size_t i = 0; i < pages_.size(); ++i)
    if (pages_[i].pending && pages_[i].generation < oldest) { page = i; oldest = pages_[i].generation; }
  if (page == pages_.size()) return false;
  Header header;
  if (!readHeader(page, header)) { fault_ = true; return false; }
  for (slot = 0; slot < pages_[page].next; ++slot)
    if (!bit(header.committed, slot) && bit(header.acknowledged, slot)) return true;
  fault_ = true; return false;
}
bool Journal::peek(Record& record) {
  size_t page; uint8_t slot;
  record = {};
  if (!locate(page, slot)) return false;
  if (!flash_->read(page * kPageBytes + kHeaderBytes + slot * pages_[page].width, &record, pages_[page].width) ||
      size(record.type) != pages_[page].width || !valid(record)) { fault_ = true; return false; }
  return true;
}
bool Journal::acknowledge(const Record& record) {
  Record oldest{};
  if (!peek(oldest) || record.session != oldest.session || record.sampleMs != oldest.sampleMs ||
      checksum(record) != checksum(oldest)) return false;
  size_t page; uint8_t slot;
  if (!locate(page, slot) || !clearBit(page, offsetof(Header, acknowledged), slot)) return false;
  --pages_[page].pending; --pending_; return true;
}
}  // namespace lil::recording
