Ans1S/esp32-c3-iot-sensor-board/Firmware/sensor/include/adc_reader.h

#pragma once

#include <Arduino.h>

#include "power_controller.h"

namespace sensor {

struct BatteryReading {
  bool valid = false;
  uint16_t millivolts = 0;
};

class AdcReader {
 public:
  void begin(PowerController& power);
  void startBatteryMeasurement();
  BatteryReading finishBatteryMeasurement(float calibrationFactor = 1.0F);
  BatteryReading readBattery(float calibrationFactor = 1.0F);

 private:
  PowerController* power_ = nullptr;
  uint32_t settleStartedUs_ = 0;
  bool measurementPending_ = false;
};

}  // namespace sensor
