Ans1S/esp32-c3-iot-sensor-board/Firmware/sensor/include/logical_clock.h

#pragma once
#include <stdint.h>

namespace sensor {
uint64_t logicalTimeUs();
inline uint64_t logicalTimeMs() { return logicalTimeUs() / 1000ULL; }
void accountForDeepSleep(uint64_t sleepMicroseconds);
}  // namespace sensor
