Ans1S/esp32-c3-iot-sensor-board/Firmware/station/include/web_pages.h

#pragma once

#include <Arduino.h>

namespace station {

extern const char kSetupWizardPage[] PROGMEM;
extern const char kLoginPage[] PROGMEM;
extern const char kDashboardPage[] PROGMEM;

}  // namespace station
