Ans1S/esp32-c3-iot-sensor-board/Firmware/tests/battery_boot_test.cpp

// Compile and execute the production setup/live/protection control flow.
#include "boot_test_platform.h"
#include "../sensor/src/main.cpp"
void testRadioTick() { ++testMillis; }
void resetBoot(bool cold = true) {
  sensorStarts = batteryReads = otaChecks = configWrites = 0;
  radioStarts = normalExchanges = lowPowerExchanges = 0;
  radioAvailable = true; stationReplies = false; powerOff = true;
  configPersistenceSucceeded = iaqClearSucceeded = true; iaqClears = 0;
  sensorStartSucceeded = true;
  sentPackets.clear(); sensor::batteries.clear();
  sensor::configurationReplies.clear();
  if (cold) { rtcState = {}; sensor::savedConfig = {}; testMillis = 100; }
  else testMillis += 86400000;
}
uint32_t boot() {
  try { setup(); } catch (const Slept& s) { return s.seconds; }
  assert(false); return 0;
}
void assertProtected() {
  assert(sensorStarts == 0 && batteryReads == 1 && powerOff);
  assert(normalExchanges == 0 && otaChecks == 0 && configWrites == 0);
  assert(lowPowerExchanges == 1 && sentPackets.size() == 1);
  const auto& p = sentPackets[0];
  assert(p.payload.operatingMode == lil::protocol::SensorOperatingMode::kBatteryProtection);
  assert(p.payload.capabilities == (lil::protocol::kPcbV4PowerGates |
      ((p.payload.flags & lil::protocol::kBatteryReadFailed) ? 0 : lil::protocol::kBattery)));
  assert(p.payload.flags & lil::protocol::kBatteryProtectionActive);
  assert(!(p.payload.flags & (lil::protocol::kSensorReadFailed | lil::protocol::kSensorTypeMismatch)));
  assert(p.payload.temperatureC == 0 && p.payload.motion.sampleCount == 0 && p.payload.live.count == 0);
  assert(lil::protocol::validate(p,sizeof(p),lil::protocol::MessageType::kTelemetry));
}
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
